fablabnk/torn/notes/DIYKeyboardPCBA/JLCPCB PCBA Viewer_files/20180914_onsemi-NCP1117LPST33T3G_C146799_front.jpg

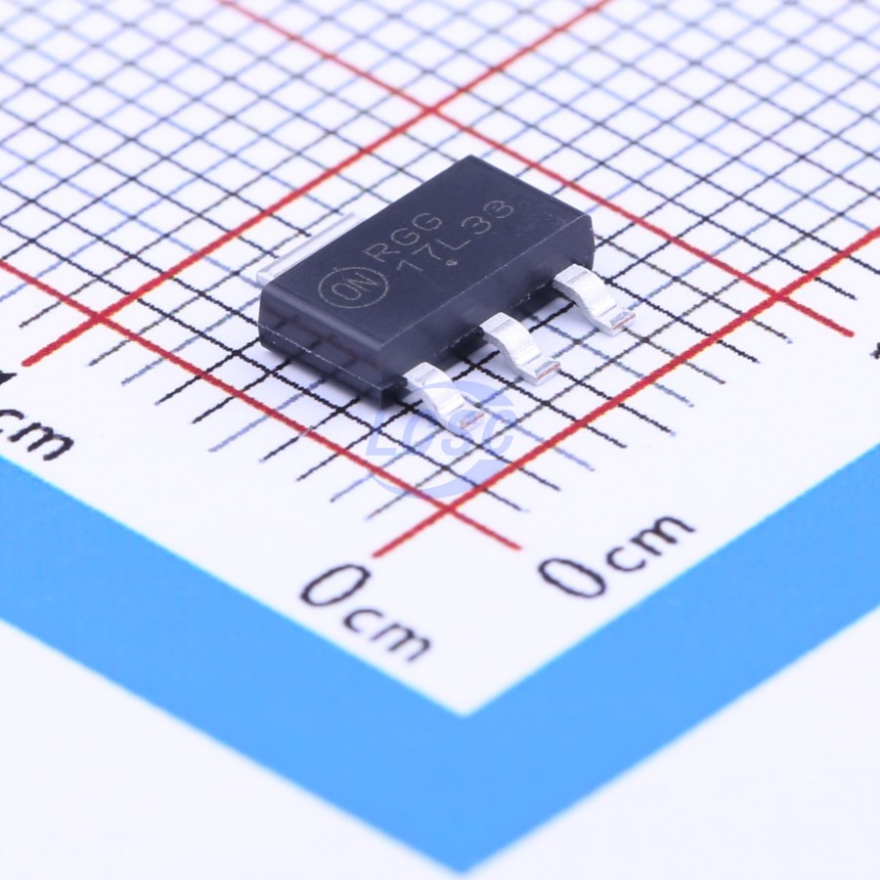
notes/DIYKeyboardPCBA/JLCPCB PCBA Viewer_files/20180914_onsemi-NCP1117LPST33T3G_C146799_front.jpg
