fablabnk/torn/notes/DIYKeyboardPCBA/JLCPCB PCBA Viewer_files/20180914_onsemi-RB521S30T1G_C145179_front.jpg

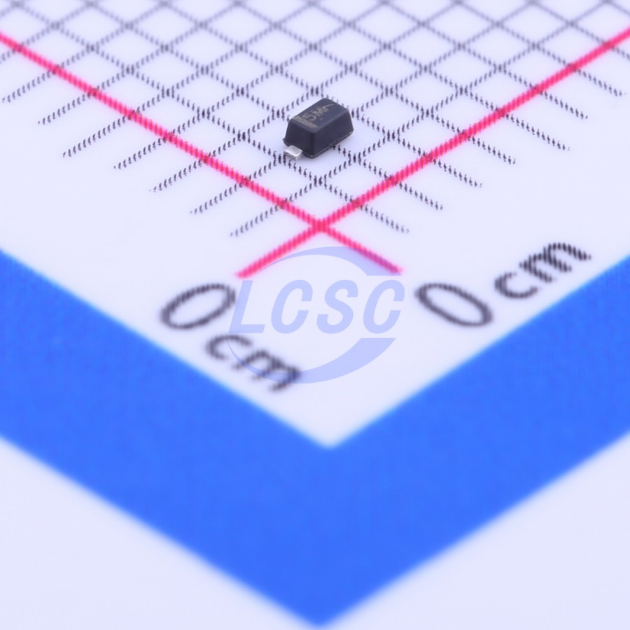
notes/DIYKeyboardPCBA/JLCPCB PCBA Viewer_files/20180914_onsemi-RB521S30T1G_C145179_front.jpg
