fablabnk/torn/notes/DIYKeyboardPCBA/JLCPCB PCBA Viewer_files/20180914_TA-I-Tech-RM04FTN5601_C156115_front.jpg

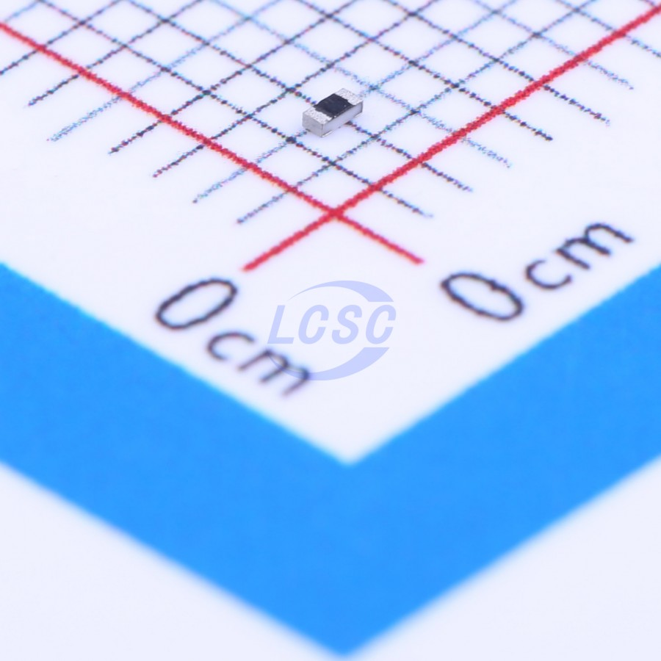
notes/DIYKeyboardPCBA/JLCPCB PCBA Viewer_files/20180914_TA-I-Tech-RM04FTN5601_C156115_front.jpg
