fablabnk/torn/notes/DIYKeyboardPCBA/JLCPCB PCBA Viewer_files/20180914_Texas-Instruments-TPD4E05U06DQAR_C138714_front.jpg

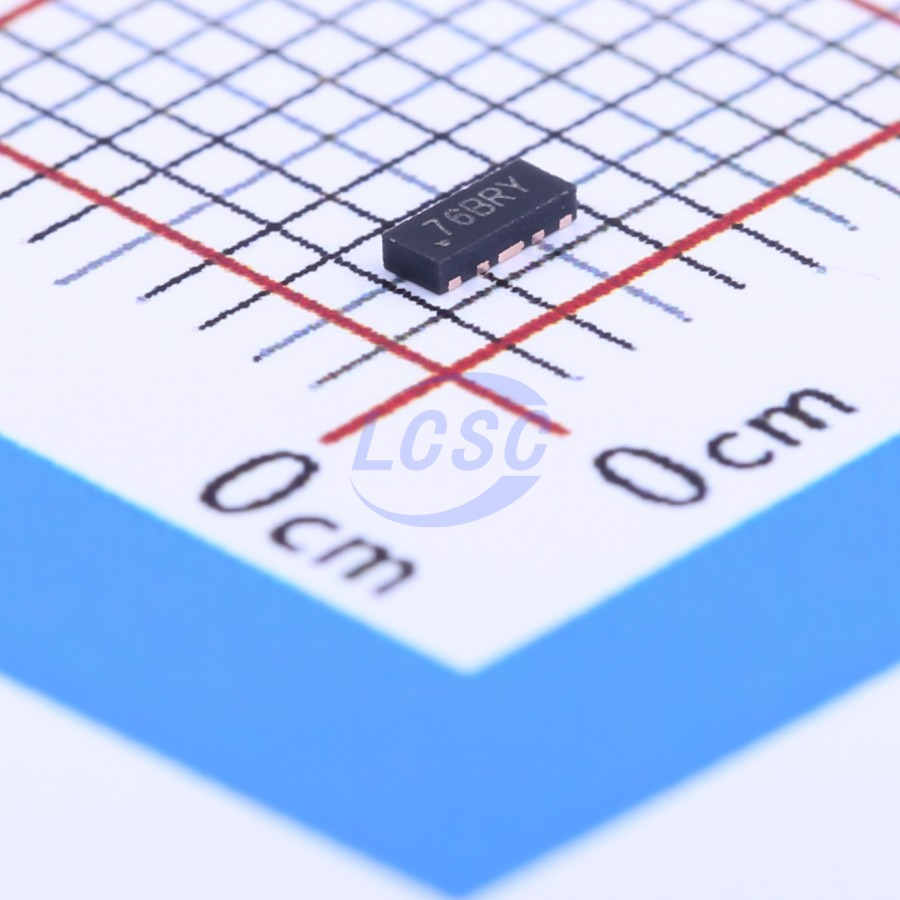
notes/DIYKeyboardPCBA/JLCPCB PCBA Viewer_files/20180914_Texas-Instruments-TPD4E05U06DQAR_C138714_front.jpg
