fablabnk/torn/notes/DIYKeyboardPCBA/JLCPCB PCBA Viewer_files/20221227_FH--Guangdong-Fenghua-Advanced-Tech-0402CG270J500NT.jpg

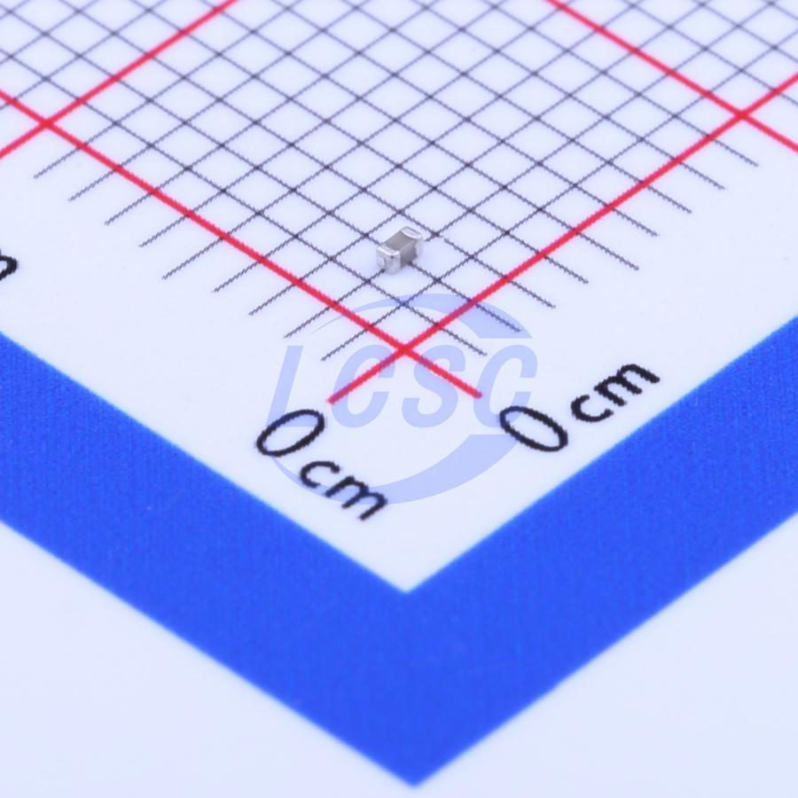
notes/DIYKeyboardPCBA/JLCPCB PCBA Viewer_files/20221227_FH--Guangdong-Fenghua-Advanced-Tech-0402CG270J500NT.jpg
