fablabnk/torn/notes/DIYKeyboardPCBA/JLCPCB PCBA Viewer_files/20221228_UNI-ROYAL-Uniroyal-Elec-0402WGF1001TCE_C11702_front.jpg

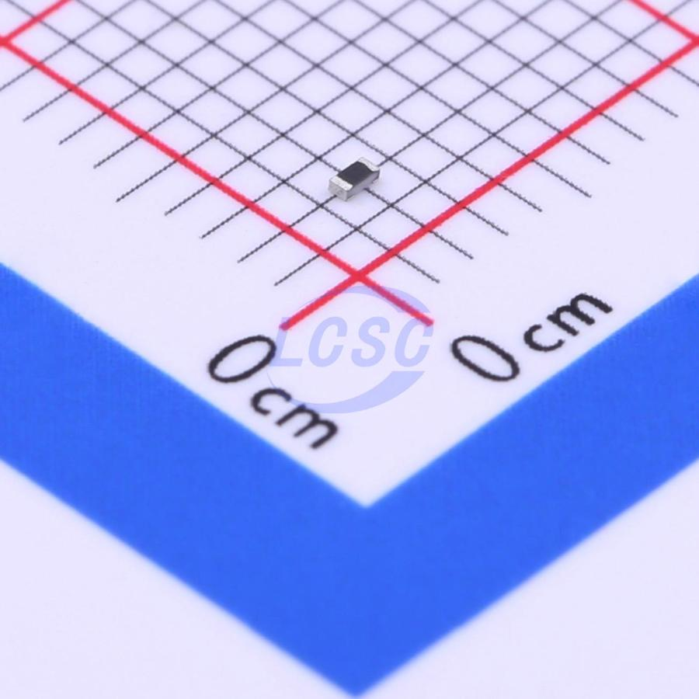
notes/DIYKeyboardPCBA/JLCPCB PCBA Viewer_files/20221228_UNI-ROYAL-Uniroyal-Elec-0402WGF1001TCE_C11702_front.jpg
