fablabnk/torn/notes/DIYKeyboardPCBA/JLCPCB PCBA Viewer_files/20221231_Seiko-Epson-Q22FA23V00418_C91749_front.jpg

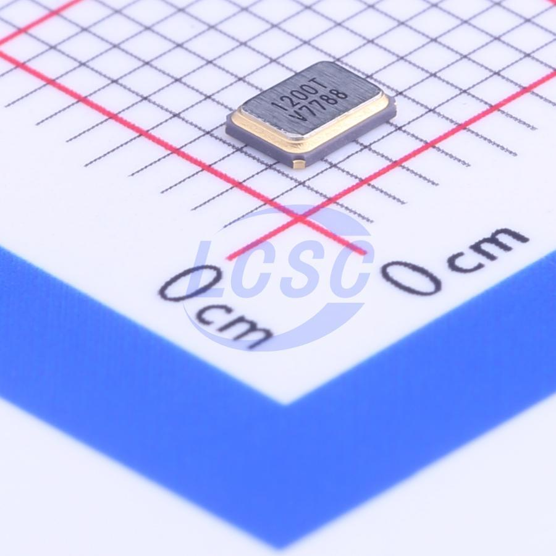
notes/DIYKeyboardPCBA/JLCPCB PCBA Viewer_files/20221231_Seiko-Epson-Q22FA23V00418_C91749_front.jpg
