fablabnk/torn/notes/DIYKeyboardPCBA/JLCPCB PCBA Viewer_files/20230102_Korean-Hroparts-Elec-PJ-399B-6A_C128994_front.jpg

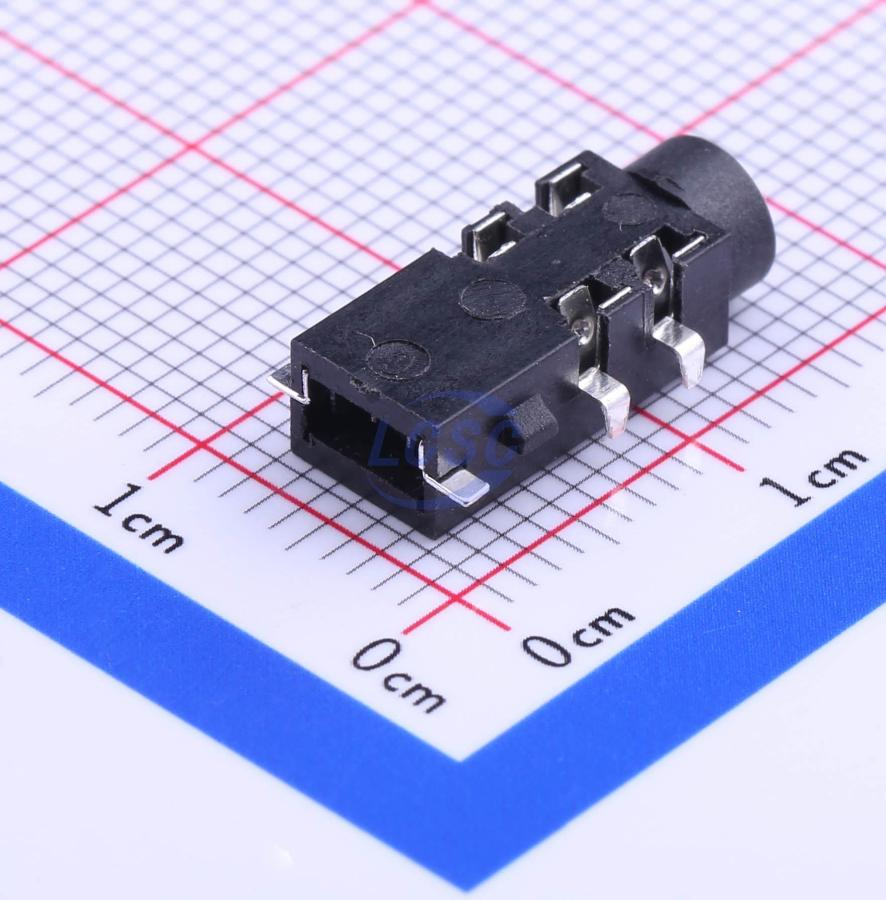
notes/DIYKeyboardPCBA/JLCPCB PCBA Viewer_files/20230102_Korean-Hroparts-Elec-PJ-399B-6A_C128994_front.jpg
