fablabnk/torn/notes/DIYKeyboardPCBA/JLCPCB PCBA Viewer_files/20230102_Winbond-Elec-W25Q128JVSIQ_C113767_front.jpg

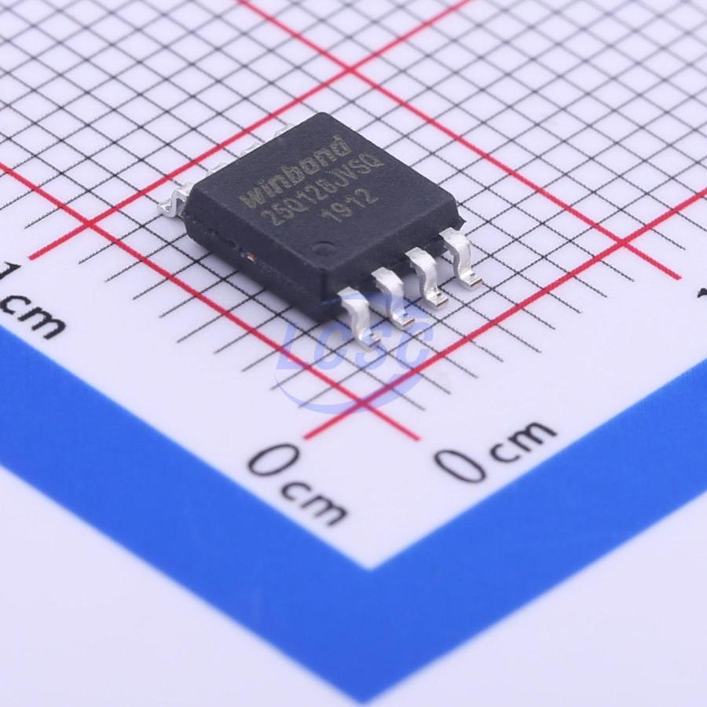
notes/DIYKeyboardPCBA/JLCPCB PCBA Viewer_files/20230102_Winbond-Elec-W25Q128JVSIQ_C113767_front.jpg
